galmasi/FressMeinGras/Arduino/Controller/ArdController/MotorControl_L298N.h

/************************************************************
 * This modules controls the L298N dual channel controller
 ************************************************************/

/* ******************* */
/* motor control state */
/* ******************* */

bool mc_stopped = true;
motorval_t mc_left    = 0;
motorval_t mc_right   = 0;
motorval_t mc_turn    = 0;

//char mc_gear   = 10;

// L298N has Motor A and Motor B
// each motor requires 3 pins
// forward,backward and pwm supplied voltage



/* *********************************************** */
/* set pin modes, and make sure motor will be stopped */
/* *********************************************** */

inline void L298N_stop(void)
{
  // set everything off
  digitalWrite(L298N_AF, LOW);
  digitalWrite(L298N_AB, LOW);
  digitalWrite(L298N_BF, LOW);
  digitalWrite(L298N_BB, LOW); 

  analogWrite(L298N_AE, 0);
  analogWrite(L298N_BE, 0);
}


inline void MotorControl_init(void) 
{
  // enable the modes of the L298N
  pinMode(L298N_AF, OUTPUT);
  pinMode(L298N_AB, OUTPUT);
  pinMode(L298N_AE, OUTPUT);
  pinMode(L298N_BF, OUTPUT);
  pinMode(L298N_BB, OUTPUT);
  pinMode(L298N_BE, OUTPUT);

  L298N_stop();
  mc_stopped = true;
}

/* *********************************************** */
/* Like every motor this has a non-linear behavior */
/* with respect to voltage supplied.               */
/* We provide a curve here to get smoother scale   */
/* *********************************************** */

char speed_to_pwm[128] = {
  // we need to get more juice to the 
  // motors to start in early 
  0, 11, 16, 20, 23, 25, 28, 30, 32, 34,
  36, 38, 39, 41, 42, 44, 45, 47, 48, 49,
  51, 52, 53, 54, 55, 57, 58, 59, 60, 61,
  62, 63, 64, 65, 66, 67, 68, 69, 70, 71,
  72, 72, 73, 74, 75, 76, 77, 78, 78, 79,
  80, 81, 82, 82, 83, 84, 85, 85, 86, 87,
  88, 88, 89, 90, 91, 91, 92, 93, 93, 94,
  95, 95, 96, 97, 97, 98, 99, 99, 100, 101,
  101, 102, 102, 103, 104, 104, 105, 106, 106, 107,
  107, 108, 109, 109, 110, 110, 111, 111, 112, 113,
  113, 114, 114, 115, 115, 116, 116, 117, 118, 118,
  119, 119, 120, 120, 121, 121, 122, 122, 123, 123,
  124, 124, 125, 125, 126, 126, 127, 127
};

#define scaleM(v) (v)  // later with gear

/* *********************************************** */
/* if motor is stopped, write zeroes.              */
/* else write state values.                        */
/* *********************************************** */

inline void MotorControl_start(void)
{
  mc_stopped = false;
  // since it was stopped all values should be
  // still set to idle
}

inline void MotorControl_stop(void)
{
  mc_stopped = true;
  mc_left = mc_right = 0;
  L298N_stop();
}

inline void MotorControl_left(motorval_t speed) 
{
  motorval_t mc_left_new, setval;

  if (mc_stopped) return; 

  mc_left_new = scaleM(speed);
  if ((mc_left_new == 0) && (mc_left == 0)) {
    digitalWrite(L298N_BB, LOW);
    digitalWrite(L298N_BF, LOW);
  } 
  else
    if ((mc_left_new >= 0) && (mc_left <= 0)) {
      digitalWrite(L298N_BB, LOW);
      digitalWrite(L298N_BF, HIGH);
    } 
    else
      if ((mc_left_new <= 0) && (mc_left >= 0)) {
        digitalWrite(L298N_BF, LOW);
        digitalWrite(L298N_BB, HIGH);
      }
  setval = abs(mc_left_new);
  analogWrite(L298N_BE, speed_to_pwm[setval]);
  mc_left = mc_left_new;
}

inline void MotorControl_right(motorval_t speed) 
{
  motorval_t mc_right_new, setval;

  if (mc_stopped) return; 

  mc_right_new = scaleM(speed);
  if ((mc_right_new==0) || (mc_right == 0)) {
    digitalWrite(L298N_AB, LOW);
    digitalWrite(L298N_AF, LOW); 
  }
  if ((mc_right_new >= 0) && (mc_right <= 0)) {
    digitalWrite(L298N_AB, LOW);
    digitalWrite(L298N_AF, HIGH);
  }
  if ((mc_right_new <= 0) && (mc_right >= 0)) {
    digitalWrite(L298N_AF, LOW);
    digitalWrite(L298N_AB, HIGH);
  }
  setval = abs(mc_right_new);
  analogWrite(L298N_AE, speed_to_pwm[setval]);
  mc_right = mc_right_new;
}

void MotorControl_turn(motorval_t turn)
{
  mc_turn = turn;  
}

#define turnscaleL(s) ((char) ((int)(s)*(128+(mc_turn))/(int)128))
#define turnscaleR(s) ((char) ((int)(s)*(128-(mc_turn))/(int)128))

void MotorControl_velocity(motorval_t speed)
{
  motorval_t lspeed, rspeed;
  lspeed = rspeed = speed;
  if (speed) {
    if (mc_turn < 0)
      lspeed = turnscaleL(speed);
    else {
      rspeed = turnscaleR(speed);
    }
  }
  MotorControl_left(lspeed);
  MotorControl_right(rspeed);
}
