galmasi/FressMeinGras/Arduino/Controller/ArdController/CommandExecutor.h

/* ******************************************************** */
/*    HOW SLOW IS SLOW?                                     */
/* ******************************************************** */
#define SLOW_LIMIT 32

/* ******************************************************** */
/* *    command executor state                            * */
/* ******************************************************** */

unsigned long _ce_lastHeartBeat;  /* timing of last heartbeat heard from BlueTooth */
motorval_t          _ce_fwLimit;        /* forward speed limit */
motorval_t          _ce_bwLimit;        /* backward speed limit */
motorval_t          _ce_turn;           /* last turn value */
motorval_t          _ce_speed;          /* last speed value */


/* ******************************************************** */
/*           initialize state                               */
/* ******************************************************** */

inline void CommandExecutor_init()
{
  _ce_lastHeartBeat = millis();
  _ce_fwLimit = 0;
  _ce_bwLimit = 0;
  _ce_turn = 0;
  _ce_speed = 0;
  Logger_log("commandexec_init", 0);
  LedLogger_set(LEDLOGGER_STOP);
}

inline motorval_t CommandExecutor_limit (motorval_t n)
{
  if (n>_ce_fwLimit) return _ce_fwLimit;
  else if (n<-_ce_bwLimit) return -_ce_bwLimit;
  else return n;
}

inline motorval_t CommandExecutor_p2r (motorval_t turn, motorval_t speed)
{
  if (turn>=0) return speed;
  else return (int)speed*((int)turn+64)/64;
}

/* ******************************************************** */
/*          enable running - remove limits.                 */
/* ******************************************************** */

inline void CommandExecutor_Go ()
{
  MotorControl_start();
  _ce_fwLimit = 127;
  _ce_bwLimit = 127;
  _ce_speed = 0;
  Logger_log ("GO", 0);
  LedLogger_set(LEDLOGGER_GO);
}

inline void CommandExecutor_Stop ()
{
  MotorControl_stop();
  _ce_fwLimit = 0;
  _ce_bwLimit = 0;
  _ce_speed = 0;
  Logger_log("STOP",0);
  LedLogger_set(LEDLOGGER_STOP);
}

// direction: 
// 1 = STOP fwd, SLOW bwd
// -1 = STOP bwd, SLOW fwd
// 0 = SLOW in both directions

void CommandExecutor_Slow(signed char dir)
{
  _ce_fwLimit = SLOW_LIMIT;
  _ce_bwLimit = SLOW_LIMIT;
  if (dir > 0) _ce_fwLimit = 0;
  if (dir < 0) _ce_bwLimit = 0;
  _ce_speed = 0;
  Logger_log("SLOW",dir);
  LedLogger_set(LEDLOGGER_SLOW);
}

inline void CommandExecutor_Left(motorval_t n)
{
  MotorControl_left (CommandExecutor_limit(n));
  Logger_log("LEFT", n);
}

inline void CommandExecutor_Right(motorval_t n)
{
  MotorControl_right (CommandExecutor_limit(n));
  Logger_log("RIGHT", n);
}

inline void CommandExecutor_Turn(motorval_t n)
{
  _ce_turn = n;
  motorval_t r = CommandExecutor_limit(CommandExecutor_p2r(-_ce_turn, _ce_speed));
  motorval_t l = CommandExecutor_limit(CommandExecutor_p2r(_ce_turn, _ce_speed));
  MotorControl_left (l);
  MotorControl_right(r);
  Logger_log("Turn", _ce_turn);
  Logger_log("Vel", _ce_speed);
  Logger_log("LEFT", l);
  Logger_log("RIGHT", r);
}

inline void CommandExecutor_Velocity(motorval_t n)
{
  _ce_speed = n;
  motorval_t r = CommandExecutor_limit(CommandExecutor_p2r(-_ce_turn, _ce_speed));
  motorval_t l = CommandExecutor_limit(CommandExecutor_p2r(_ce_turn, _ce_speed));
  MotorControl_left (l);
  MotorControl_right(r);
  Logger_log("Turn", _ce_turn);
  Logger_log("Vel", _ce_speed);
  Logger_log("LEFT", l);
  Logger_log("RIGHT", r);  
}

inline void CommandExecutor_Ping ()
{
}

inline void CommandExecutor_HeartBeat()
{
  // we send the heartbeat every 750msec in case no commands are coming
  // from the controller.
  // Any command should be taken as a heartbeat, so move the hearbeat
  // outside this case statement
  if (_ce_lastHeartBeat == 0) CommandExecutor_Stop();
  _ce_lastHeartBeat = millis();
  Logger_log("commandexec_heartbeat", 0);
}

/* ********************************g************************ */
/*          update LEDs, check heartbeat etc.               */
/* ******************************************************** */
inline void CommandExecutor_loop()
{
  // we expect a heartbeat to be send every 750msec
  // the 1000msec check provides some slack
#ifdef HAVE_HEARTBEAT
  if (millis() > (_ce_lastHeartBeat + 1000)) {
    // we lost communication with RC
    if (_ce_lastHeartBeat>0) {
      CommandExecutor_Stop();
      Logger_log("No heartbeat", 0);
      LedLogger_set(LEDLOGGER_NOHEARTBEAT);
    }
    _ce_lastHeartBeat=0;
  }
#endif
}
